protospacenl/BodySenseArray/hw/footprints/tagconnect/KiCad/Tag-Connect Full Catalog KiCad Decal Library/Tag-Connect_DemoBoard/Tag-Connect_DemoBoard.sch

## KiCad design hw/footprints/tagconnect/KiCad/Tag-Connect Full Catalog KiCad Decal Library/Tag-Connect_DemoBoard/Tag-Connect_DemoBoard.sch (2019-06-06)

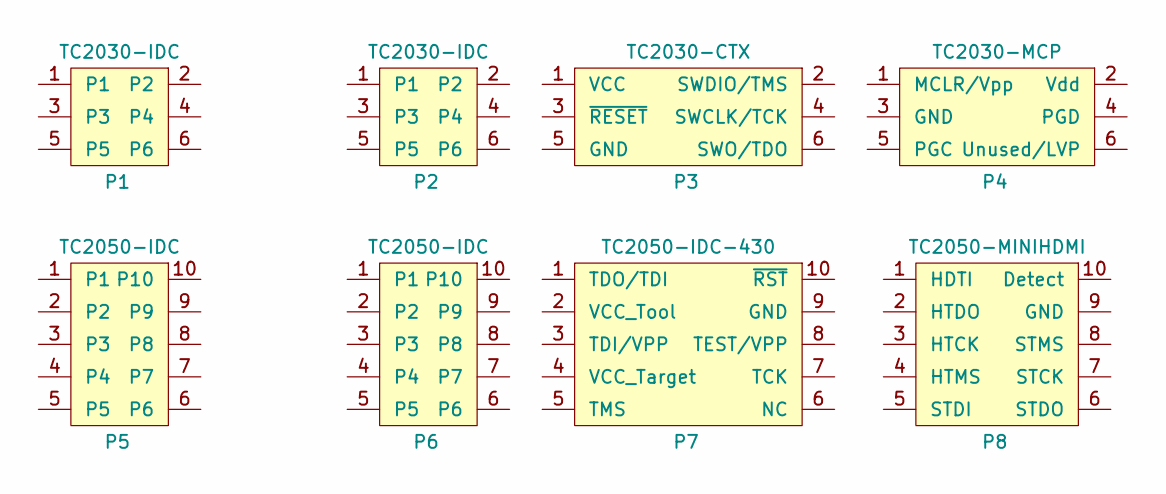
[picture p3: schematic Tag-Connect_DemoBoard.sch]

Parts:
P1, P2: TC2030-IDC
P3: TC2030-CTX
P4: TC2030-MCP
P5, P6: TC2050-IDC
P7: TC2050-IDC-430
P8: TC2050-MINIHDMI
